mszczesniak02/eit_internship/Poseidon_pump/models_pumps/pump/syringe_latch.stl

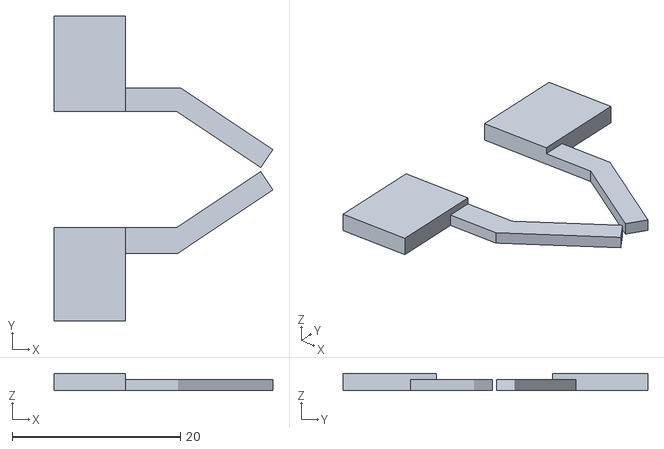
[picture p13: CAD file, 2025-08-06]
Poseidon_pump/models_pumps/pump/syringe_latch.stl
26.0 x 36.3 x 2.05
