mszczesniak02/eit_internship/Poseidon_pump/code/HARDWARE/pump/step/Pump Syringe Brace.step

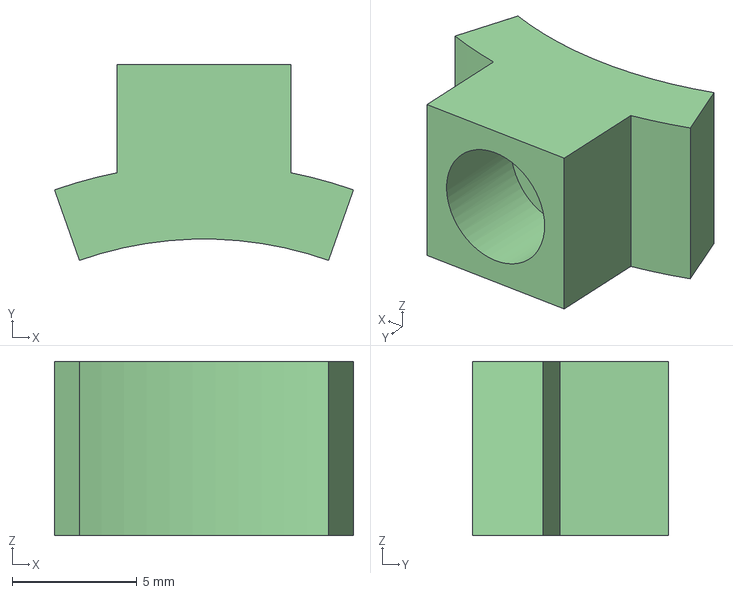
[picture p14: CAD file, 2025-08-06]
Poseidon_pump/code/HARDWARE/pump/step/Pump Syringe Brace.step
12.0 x 7.86 x 7.00 mm
