mszczesniak02/eit_internship/Poseidon_pump/models_pumps/pump/pump_3_carriage.stl

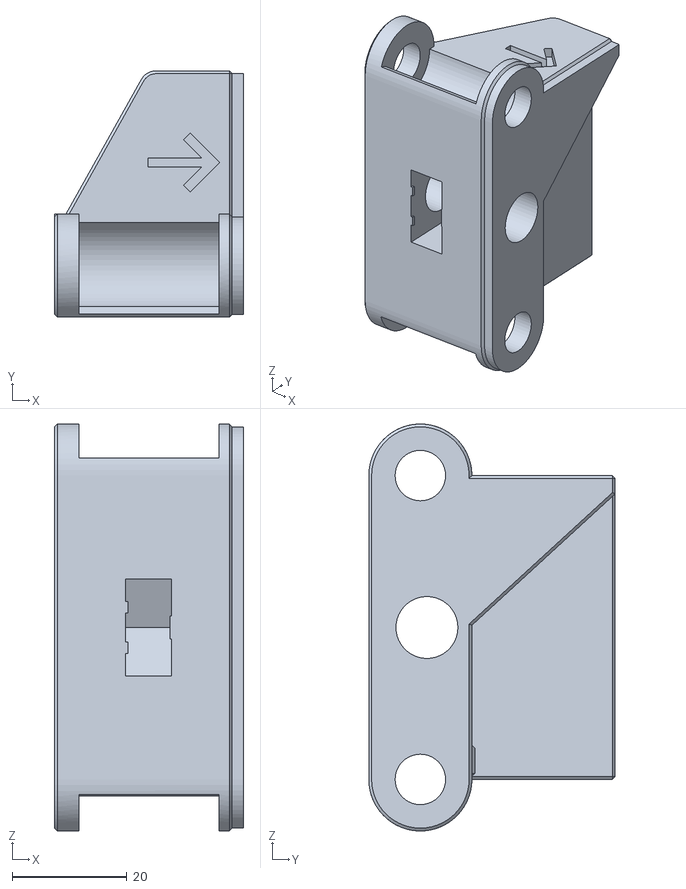
[picture p15: CAD file, 2025-08-06]
Poseidon_pump/models_pumps/pump/pump_3_carriage.stl
33.0 x 43.0 x 71.0
